X-Illuminati/SNES-clickety-clacker/doc/20170204-SNES Controller Mech.jpg

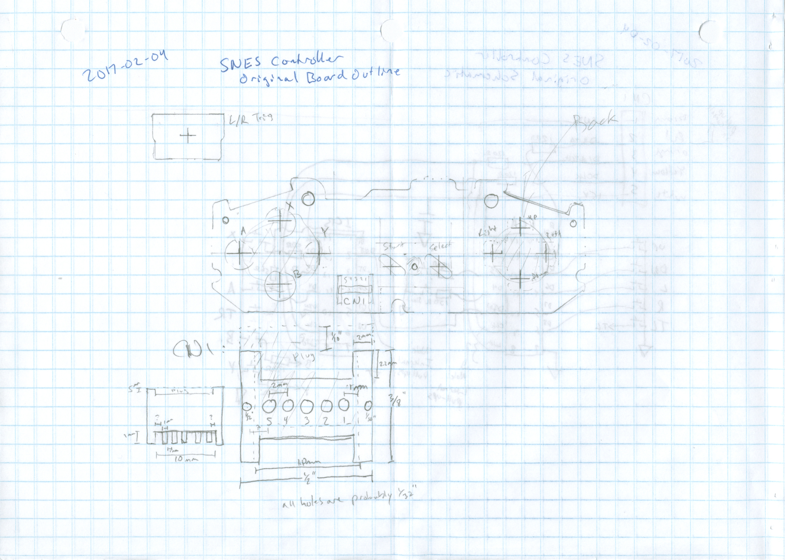
doc/20170204-SNES Controller Mech.jpg
