X-Illuminati/SNES-clickety-clacker/doc/SNES_controller_LR.png

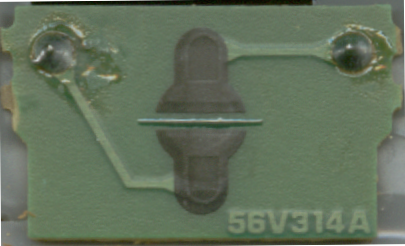
doc/SNES_controller_LR.png
